beulard/lard84/screenshots/case-v6-with-pcb.png

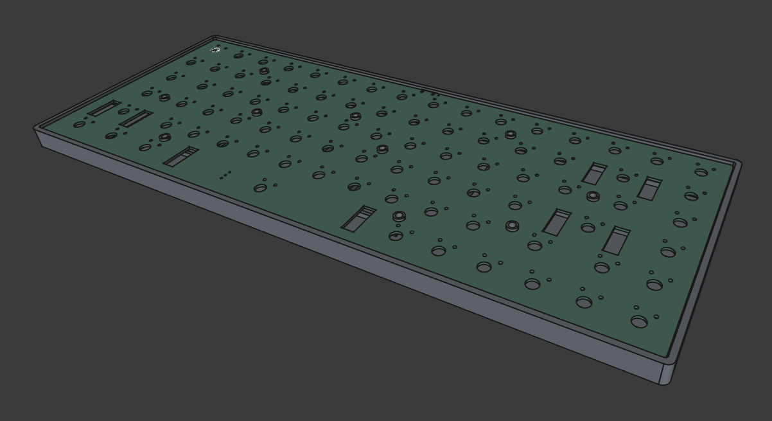
screenshots/case-v6-with-pcb.png
