beulard/lard84/screenshots/lard84-pcb-2-back.png

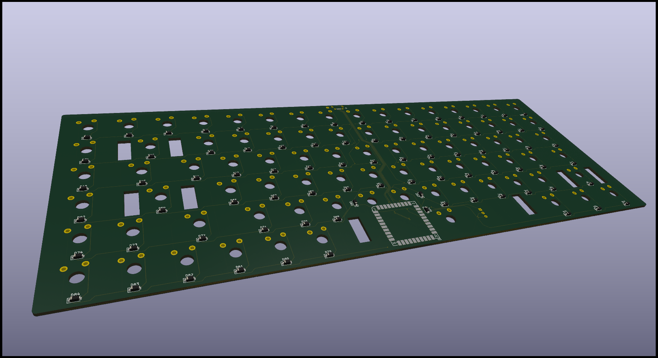
screenshots/lard84-pcb-2-back.png
