beulard/lard84/screenshots/lard84-v1.0-angle.png

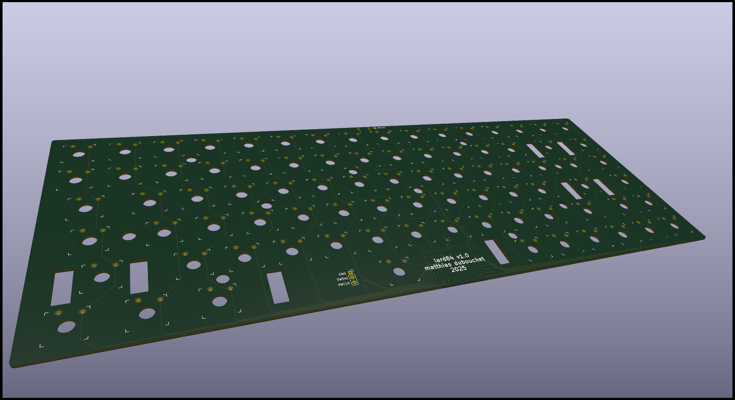
screenshots/lard84-v1.0-angle.png
