beulard/lard84/screenshots/plate-only-face.png

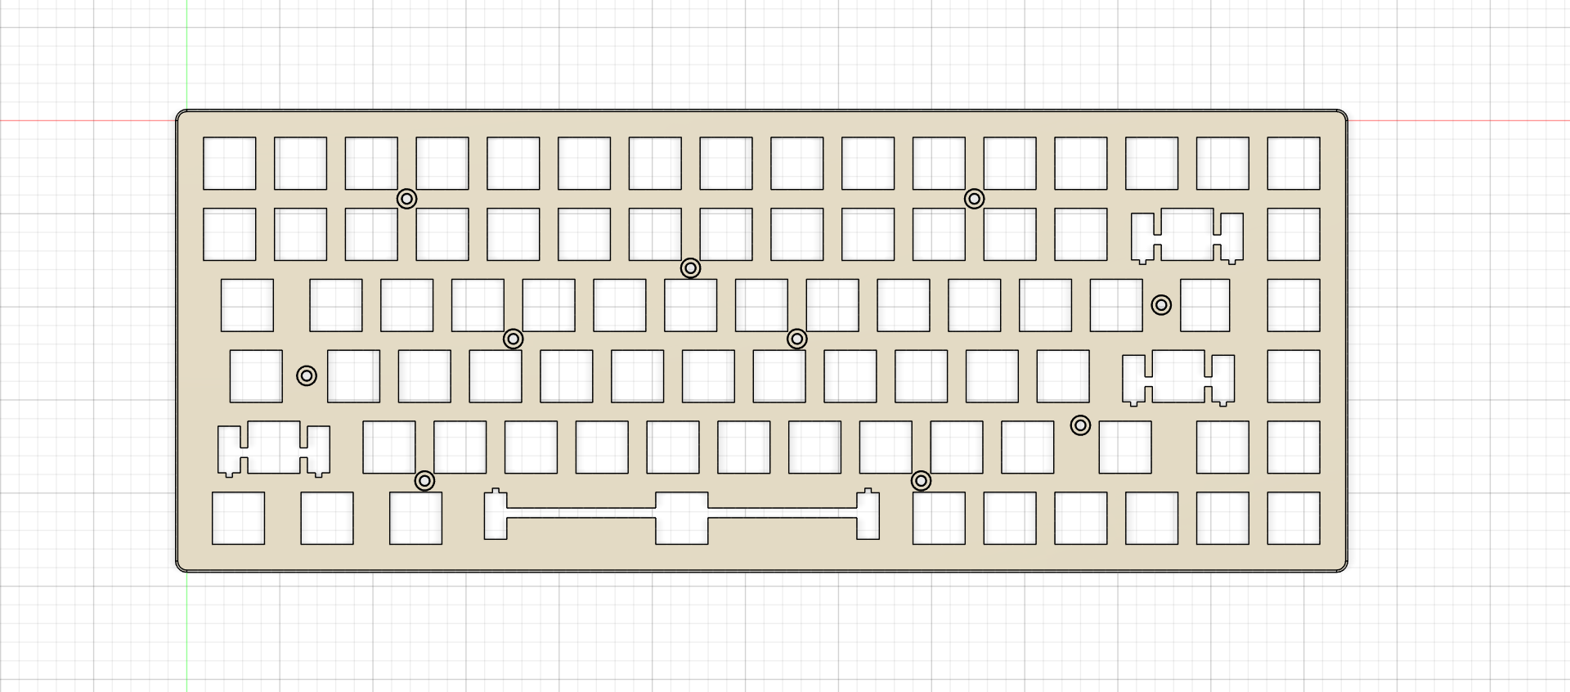
screenshots/plate-only-face.png
